martinberlin/bistable-smart-switch/Hardware/C3-27-epaper-touch/parts/3d/CR1220-2.step

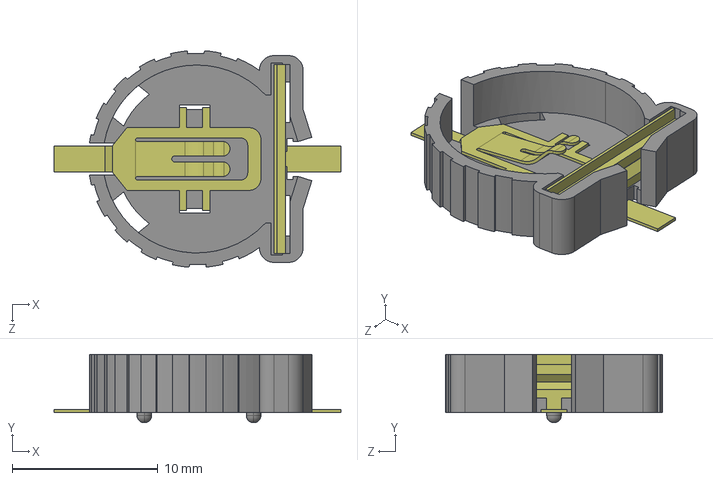
[picture p18: CAD file, 2023-02-20]
Hardware/C3-27-epaper-touch/parts/3d/CR1220-2.step
19.7 x 4.70 x 14.9 mm
