martinberlin/bistable-smart-switch/Hardware/C3-27-epaper-touch/parts/3d/IND_0S282MT_SNL.step

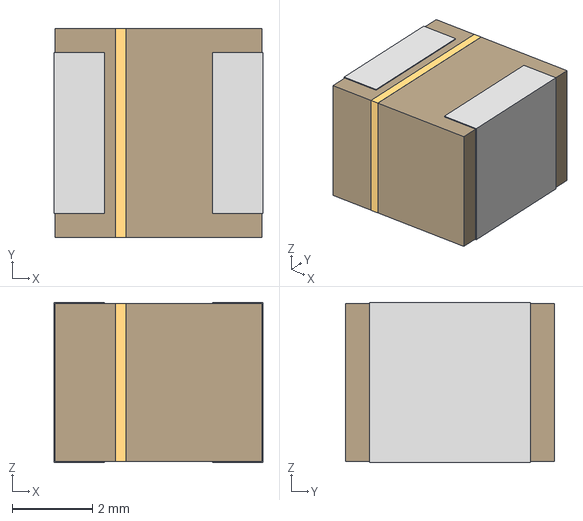
[picture p19: CAD file, 2023-02-20]
Hardware/C3-27-epaper-touch/parts/3d/IND_0S282MT_SNL.step
5.21 x 5.21 x 3.99 mm
