martinberlin/bistable-smart-switch/Hardware/C3-27-epaper-touch/parts/3d/ESP32-C3-WROOM-02-H4.step

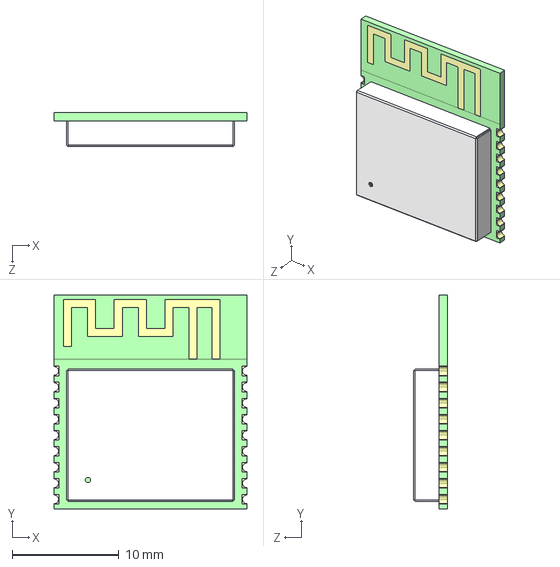
[picture p20: CAD file, 2023-02-20]
Hardware/C3-27-epaper-touch/parts/3d/ESP32-C3-WROOM-02-H4.step
18.0 x 20.0 x 3.20 mm
