martinberlin/bistable-smart-switch/Hardware/C3-27-epaper-touch/parts/3d/L-40xx.STEP

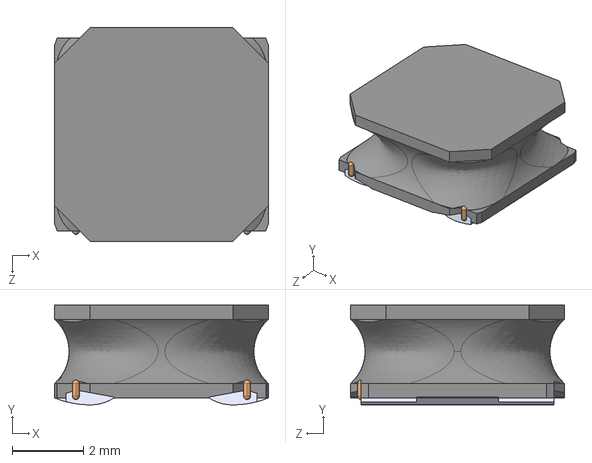
[picture p21: CAD file, 2023-02-20]
Hardware/C3-27-epaper-touch/parts/3d/L-40xx.STEP
6.00 x 2.80 x 6.00 mm
