martinberlin/bistable-smart-switch/Hardware/C3-27-epaper-touch/parts/3d/HRO_TYPE-C-31-M-12.step

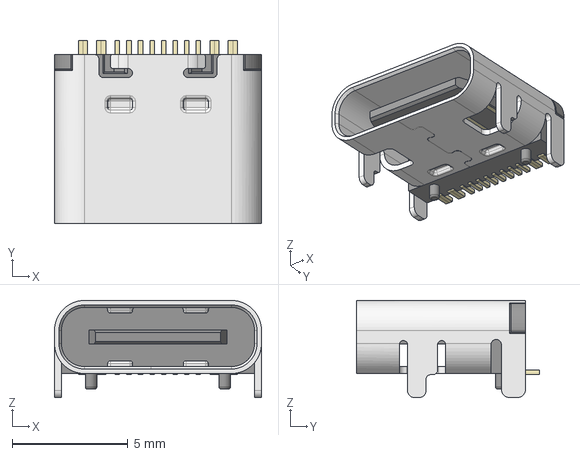
[picture p22: CAD file, 2023-02-20]
Hardware/C3-27-epaper-touch/parts/3d/HRO_TYPE-C-31-M-12.step
8.95 x 7.90 x 4.20 mm
