martinberlin/bistable-smart-switch/Hardware/C3-27-epaper-touch/parts/3d/CP2102N-A02-GQFN28R.step

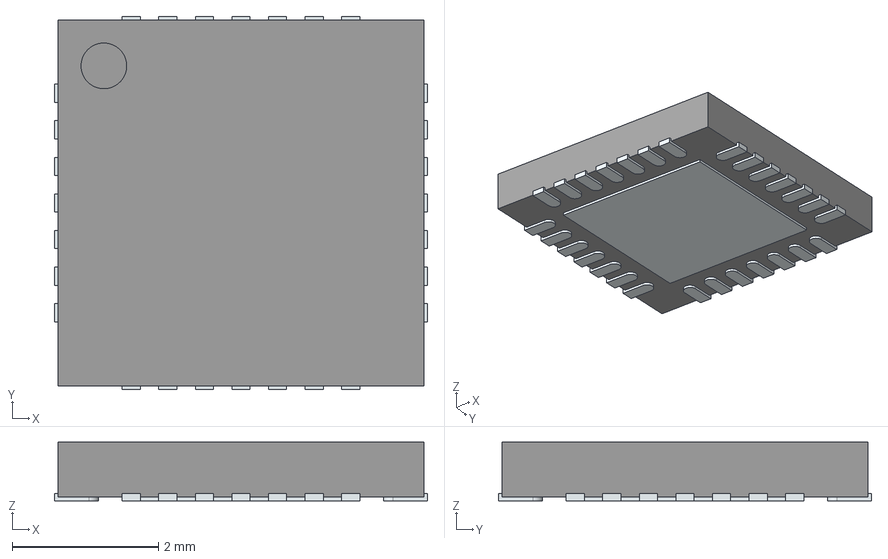
[picture p23: CAD file, 2023-02-20]
Hardware/C3-27-epaper-touch/parts/3d/CP2102N-A02-GQFN28R.step
5.10 x 5.10 x 0.8 mm
ThermalPin
PinsArrayLR
PinsArrayTB
