martinberlin/bistable-smart-switch/Hardware/C3-27-epaper-touch/parts/3d/c-5-1676966-1-ba-3d.stp

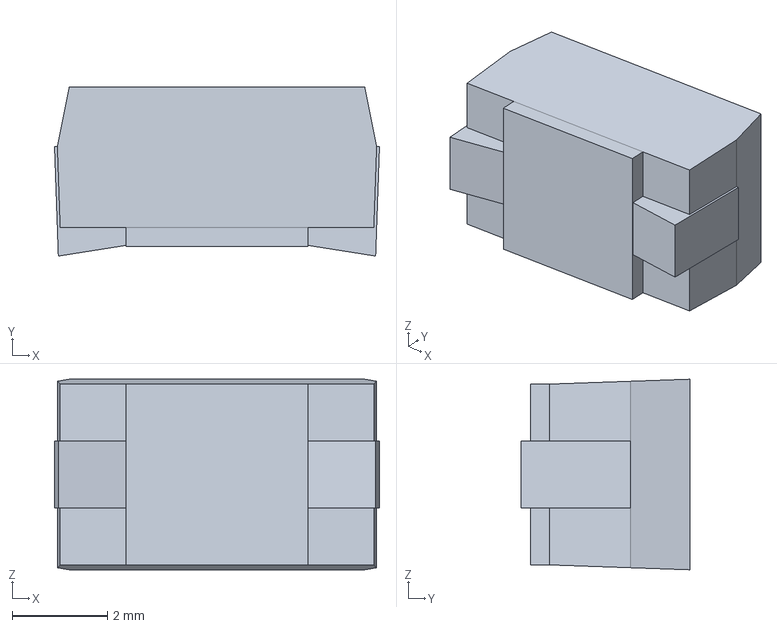
[picture p24: CAD file, 2023-02-18]
Hardware/C3-27-epaper-touch/parts/3d/c-5-1676966-1-ba-3d.stp
6.82 x 3.55 x 4.00 mm
