martinberlin/bistable-smart-switch/Hardware/C3-27-epaper-touch/parts/3d/0443Series_LTF.step

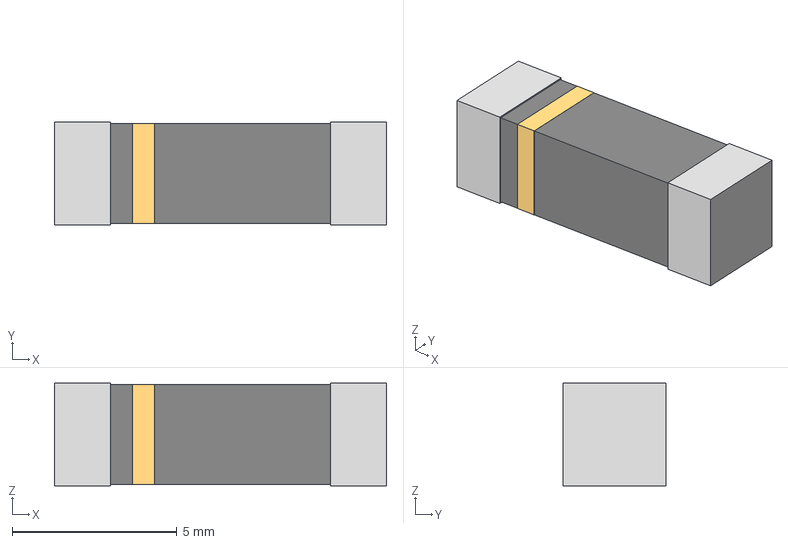
[picture p25: CAD file, 2023-02-18]
Hardware/C3-27-epaper-touch/parts/3d/0443Series_LTF.step
10.1 x 3.12 x 3.12 mm
